megabitsenmzq/MyVFD/Code/include/bitmap.h

#ifndef BITMAP_H
#define BITMAP_H

#include <stdint.h>
const uint8_t loadingAnimation[6] = { 0x01, 0x02, 0x04, 0x08, 0x10, 0x20 };
const uint8_t loadingAnimationLenth = 6;

const uint8_t screenTestingAnimation[17][9] = {
  // Digits
  { 0xff, 0x00, 0x00, 0x00, 0x00, 0x00, 0x00, 0x00, 0x00 },
  { 0x00, 0xff, 0x00, 0x00, 0x00, 0x00, 0x00, 0x00, 0x00 },
  { 0x00, 0x00, 0xff, 0x00, 0x00, 0x00, 0x00, 0x00, 0x00 },
  { 0x00, 0x00, 0x00, 0xff, 0x00, 0x00, 0x00, 0x00, 0x00 },
  { 0x00, 0x00, 0x00, 0x00, 0xff, 0x00, 0x00, 0x00, 0x00 },
  { 0x00, 0x00, 0x00, 0x00, 0x00, 0xff, 0x00, 0x00, 0x00 },
  { 0x00, 0x00, 0x00, 0x00, 0x00, 0x00, 0xff, 0x00, 0x00 },
  { 0x00, 0x00, 0x00, 0x00, 0x00, 0x00, 0x00, 0xff, 0x00 },
  { 0x00, 0x00, 0x00, 0x00, 0x00, 0x00, 0x00, 0x00, 0xff },
  // Segments
  { 0x01, 0x01, 0x01, 0x01, 0x01, 0x01, 0x01, 0x01, 0x01 },
  { 0x02, 0x02, 0x02, 0x02, 0x02, 0x02, 0x02, 0x02, 0x02 },
  { 0x04, 0x04, 0x04, 0x04, 0x04, 0x04, 0x04, 0x04, 0x04 },
  { 0x08, 0x08, 0x08, 0x08, 0x08, 0x08, 0x08, 0x08, 0x08 },
  { 0x10, 0x10, 0x10, 0x10, 0x10, 0x10, 0x10, 0x10, 0x10 },
  { 0x20, 0x20, 0x20, 0x20, 0x20, 0x20, 0x20, 0x20, 0x20 },
  { 0x40, 0x40, 0x40, 0x40, 0x40, 0x40, 0x40, 0x40, 0x40 },
  { 0x80, 0x80, 0x80, 0x80, 0x80, 0x80, 0x80, 0x80, 0x80 }
};
const uint8_t screenTestingAnimationLenth = 17;

#endif
